LEN-J-S/Emergency-Crew-Transport-Litter-for-Space/HAND SKETCHES/1.jpg

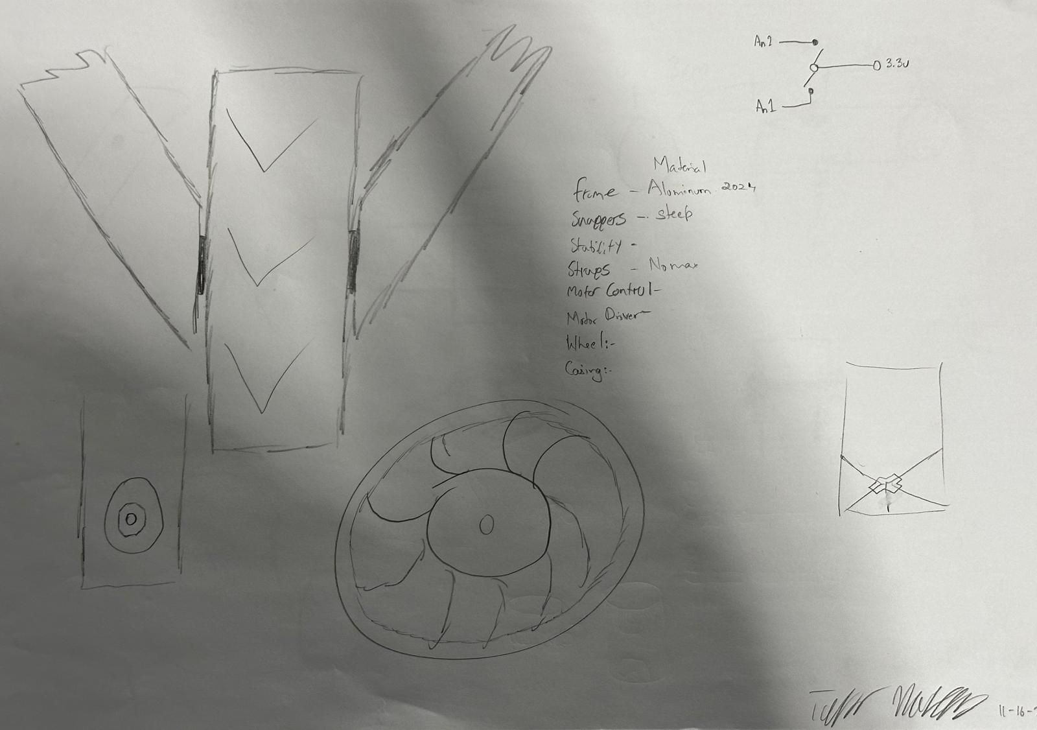
HAND SKETCHES/1.jpg
