LEN-J-S/Emergency-Crew-Transport-Litter-for-Space/HAND SKETCHES/2.jpg

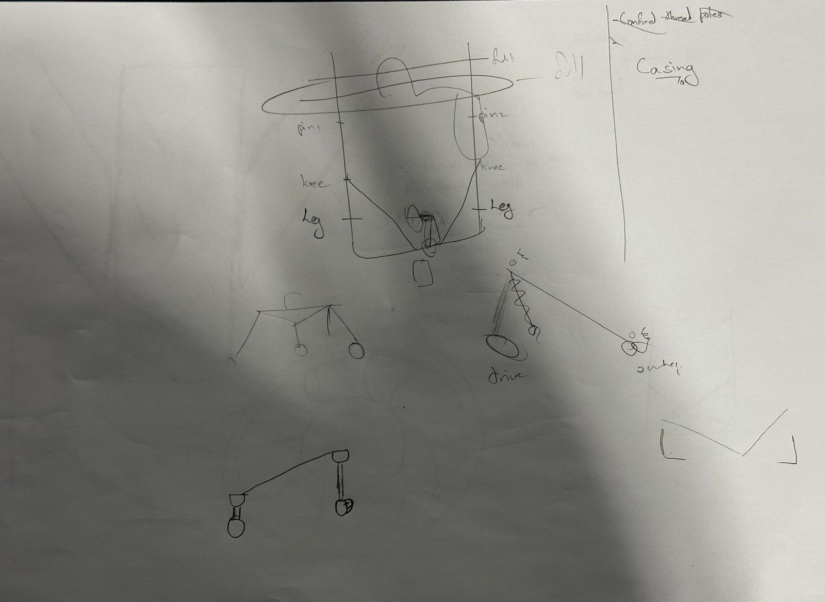
HAND SKETCHES/2.jpg
