LEN-J-S/Emergency-Crew-Transport-Litter-for-Space/HAND SKETCHES/3.jpg

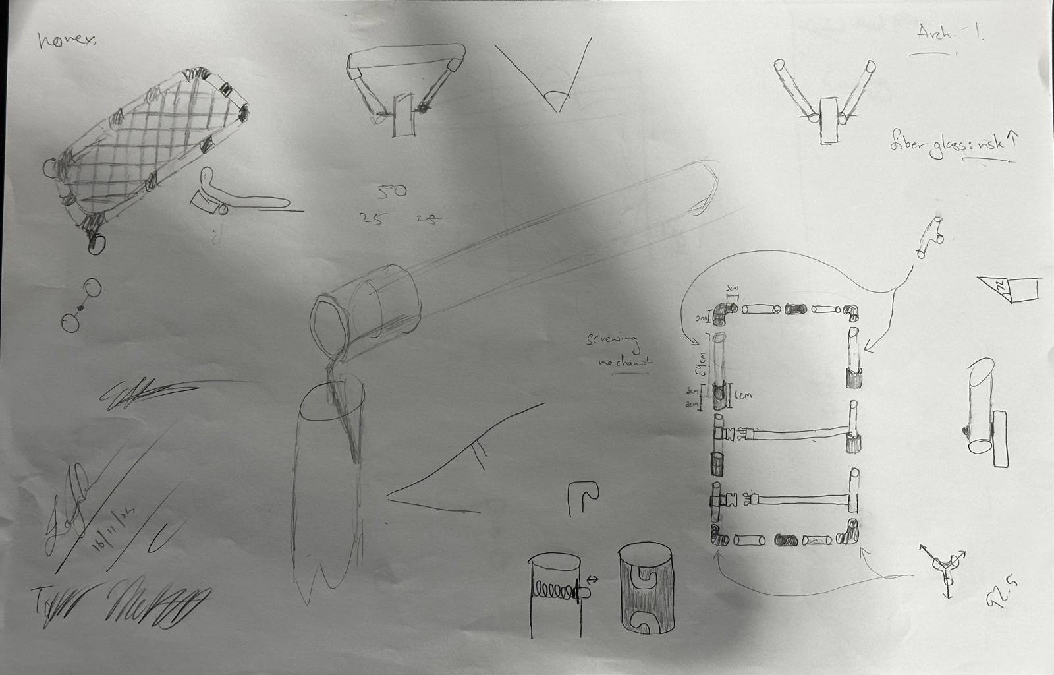
HAND SKETCHES/3.jpg
