LEN-J-S/Emergency-Crew-Transport-Litter-for-Space/HAND SKETCHES/4.jpg

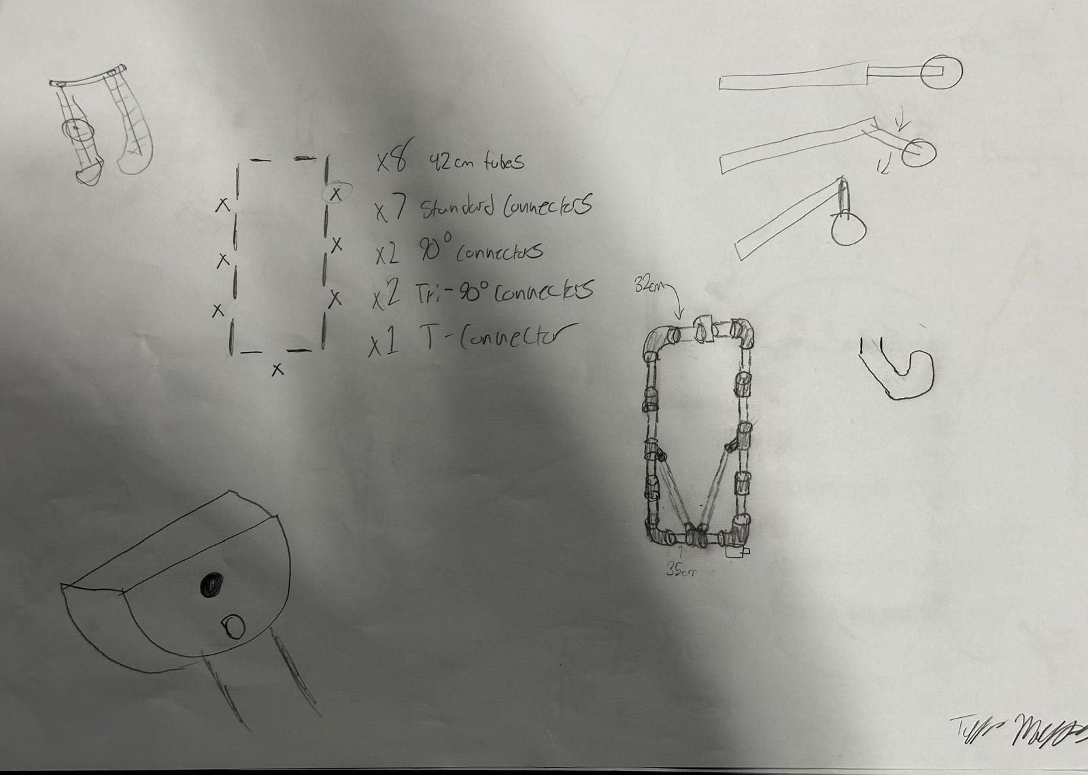
HAND SKETCHES/4.jpg
