LEN-J-S/Emergency-Crew-Transport-Litter-for-Space/HAND SKETCHES/B1.jpg

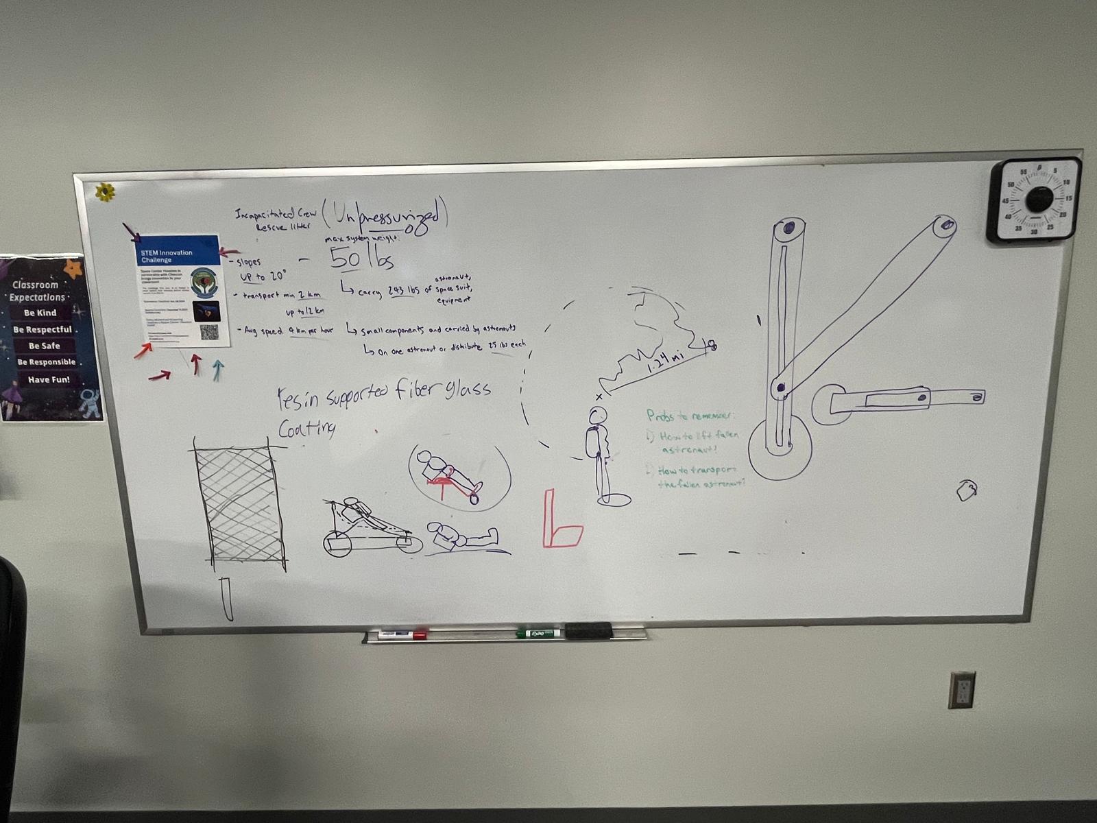
HAND SKETCHES/B1.jpg
