LEN-J-S/Emergency-Crew-Transport-Litter-for-Space/CAD FILES/casing.SLDPRT

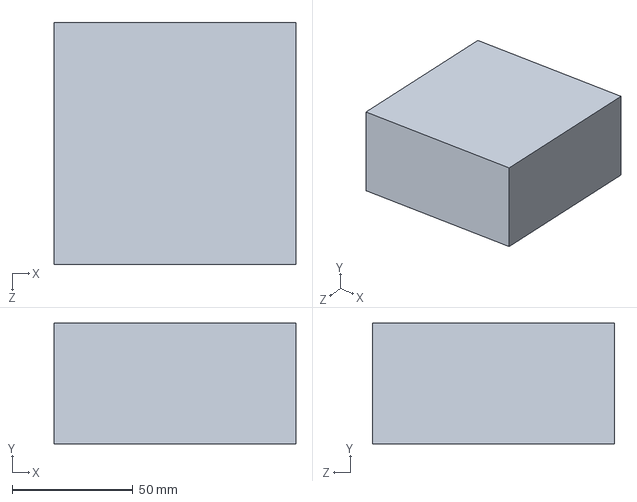
[picture p44: CAD file, 2025-04-19]
CAD FILES/casing.SLDPRT
100.0 x 50.0 x 100.0 mm
