LEN-J-S/Emergency-Crew-Transport-Litter-for-Space/CAD FILES/Straight pipe.SLDPRT

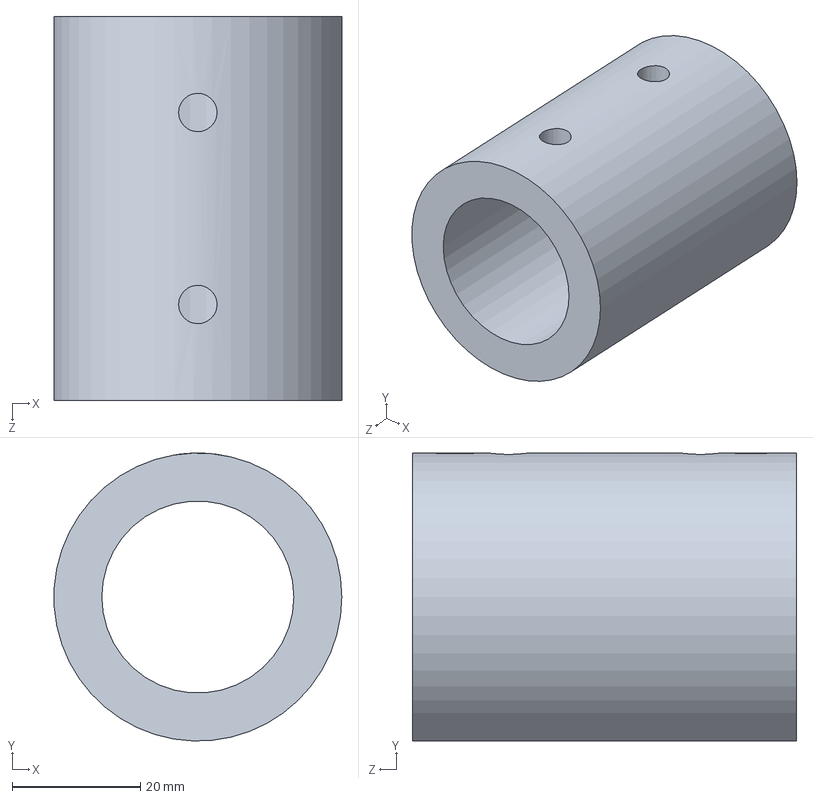
[picture p45: CAD file, 2025-04-19]
CAD FILES/Straight pipe.SLDPRT
44.9 x 45.0 x 60.0 mm
