LEN-J-S/Emergency-Crew-Transport-Litter-for-Space/CAD FILES/Pole to tire.SLDPRT

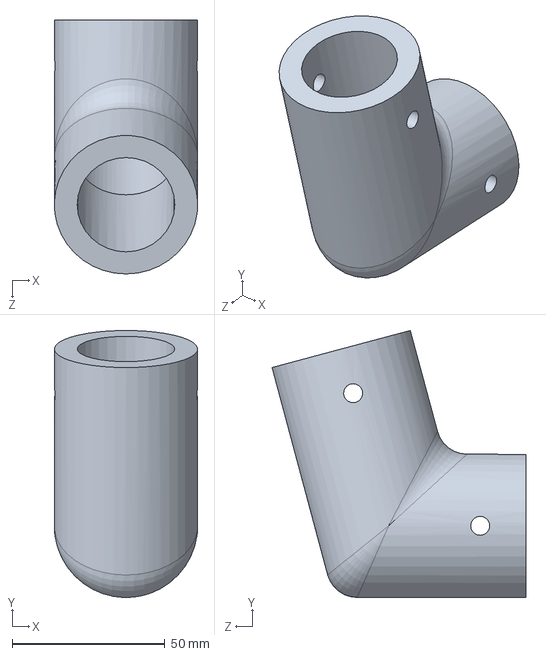
[picture p46: CAD file, 2025-04-19]
CAD FILES/Pole to tire.SLDPRT
47.0 x 87.5 x 83.2 mm
