LEN-J-S/Emergency-Crew-Transport-Litter-for-Space/CAD FILES/Front wheel pivot connector.SLDPRT

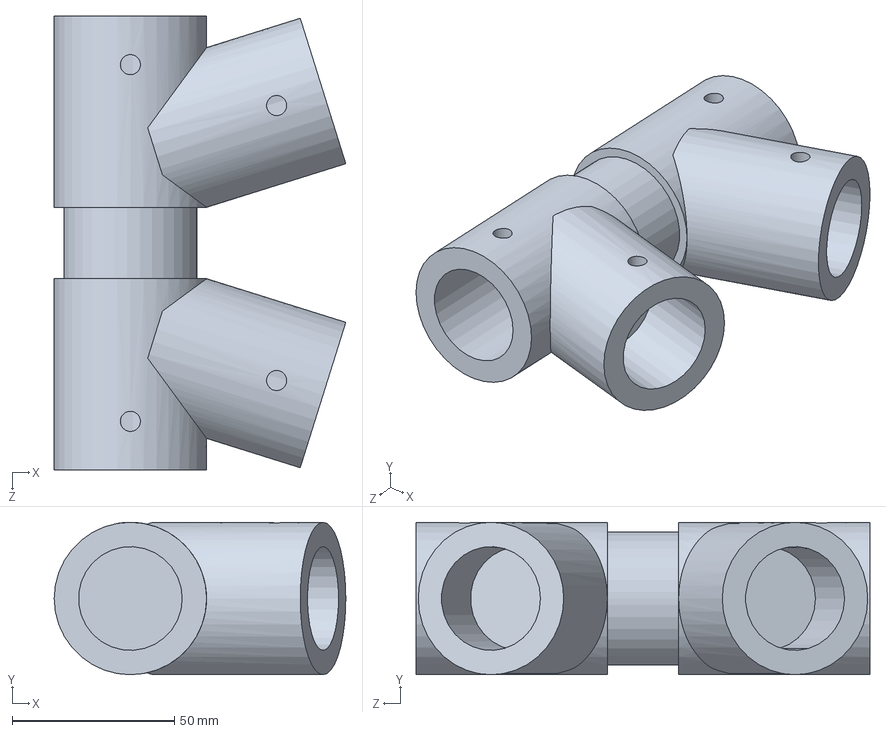
[picture p47: CAD file, 2025-04-19]
CAD FILES/Front wheel pivot connector.SLDPRT
89.9 x 47.0 x 140.0 mm
